MetaWu2077/Esp32_VoiceChat_LLMs/developboard/SmartAssistant-board/src/main/Audio1.cpp

#include "Audio1.h"

Audio1::Audio1()
{
  // 构造函数中仅做基本的初始化，不分配大块内存或其他可能引起问题的操作
  wavData = nullptr;
  i2s = nullptr;
  i2s = new I2S();

  // wavData = new char*[wavDataSize/dividedWavDataSize];
  // for (int i = 0; i < wavDataSize/dividedWavDataSize; ++i) wavData[i] = new char[dividedWavDataSize];
  // i2s = new I2S(micType);
}

Audio1::~Audio1()
{
  for (int i = 0; i < wavDataSize / dividedWavDataSize; ++i)
    delete[] wavData[i];
  delete[] wavData;
  delete i2s;
}

void Audio1::init()
{
  wavData = new char *[1];
  for (int i = 0; i < 1; ++i)
    wavData[i] = new char[1280];
}

void Audio1::clear()
{
  i2s->clear();
}

void Audio1::CreateWavHeader(byte *header, int waveDataSize)
{
  header[0] = 'R';
  header[1] = 'I';
  header[2] = 'F';
  header[3] = 'F';
  unsigned int fileSizeMinus8 = waveDataSize + 44 - 8;
  header[4] = (byte)(fileSizeMinus8 & 0xFF);
  header[5] = (byte)((fileSizeMinus8 >> 8) & 0xFF);
  header[6] = (byte)((fileSizeMinus8 >> 16) & 0xFF);
  header[7] = (byte)((fileSizeMinus8 >> 24) & 0xFF);
  header[8] = 'W';
  header[9] = 'A';
  header[10] = 'V';
  header[11] = 'E';
  header[12] = 'f';
  header[13] = 'm';
  header[14] = 't';
  header[15] = ' ';
  header[16] = 0x10; // linear PCM
  header[17] = 0x00;
  header[18] = 0x00;
  header[19] = 0x00;
  header[20] = 0x01; // linear PCM
  header[21] = 0x00;
  header[22] = 0x01; // monoral
  header[23] = 0x00;
  header[24] = 0x80; // sampling rate 16000
  header[25] = 0x3E;
  header[26] = 0x00;
  header[27] = 0x00;
  header[28] = 0x00; // Byte/sec = 16000x2x1 = 32000
  header[29] = 0x7D;
  header[30] = 0x00;
  header[31] = 0x00;
  header[32] = 0x02; // 16bit monoral
  header[33] = 0x00;
  header[34] = 0x10; // 16bit
  header[35] = 0x00;
  header[36] = 'd';
  header[37] = 'a';
  header[38] = 't';
  header[39] = 'a';
  header[40] = (byte)(waveDataSize & 0xFF);
  header[41] = (byte)((waveDataSize >> 8) & 0xFF);
  header[42] = (byte)((waveDataSize >> 16) & 0xFF);
  header[43] = (byte)((waveDataSize >> 24) & 0xFF);
}

void Audio1::Record()
{

  i2s->Read(i2sBuffer, i2sBufferSize);
  for (int i = 0; i < i2sBufferSize / 8; ++i)
  {
    wavData[0][2 * i] = i2sBuffer[8 * i + 2];
    wavData[0][2 * i + 1] = i2sBuffer[8 * i + 3];
  }

  // client.print("\r\n");

  // unsigned long startTime = millis();
  // while (_client->available() == 0)
  // {
  //   if (millis() - startTime > 5000)
  //   { // 5莽钮聣膰聨聲莽搂麓茅聫聝膹偶?
  //     Serial.println(">>> Client Timeout!");
  //     _client->stop();
  //     return "false";
  //   }
  // }
  // // Serial.println("123");
  // char c = 0;
  // int q = 0;

  // if (_client->available())
  // {
  //   String response = _client->readString();

  //   Serial.println(response);

  //   int jsonStartIndex = response.indexOf("\r\n\r\n") + 4;
  //   String jsonResponse = response.substring(jsonStartIndex);

  //   Question = parseJSON(jsonResponse.c_str());
  //   // int len = Question.length();
  //   // Question = Question.substring(0, (len - 1));
  //   // Question = "\"" + Question + "\"";
  //   Serial.println(Question);
  // }

  // Serial.println("456");

  // _client->stop();
  // return Question;
}

String Audio1::parseJSON(const char *jsonResponse)
{
  DynamicJsonDocument doc(1024);

  // 瑙ｆ瀽JSON鍝嶅簲
  DeserializationError error = deserializeJson(doc, jsonResponse);
  if (error)
  {
    Serial.print(F("deserializeJson() failed: "));
    Serial.println(error.f_str());
    return String("");
  }

  // 鎻愬彇骞惰繑鍥?"question"
  const char *question = doc["result"][0];
  return String(question);
}

float Audio1::calculateRMS(uint8_t *buffer, int bufferSize)
{
  float sum = 0;
  int16_t sample;

  // 每次迭代处理两个字节（16位）
  for (int i = 0; i < bufferSize; i += 2)
  {
    // 从缓冲区中获取16位样本，考虑到字节顺序
    sample = (buffer[i + 1] << 8) | buffer[i];

    // 计算样本的平方并累加
    sum += sample * sample;
  }

  // 计算平均值
  sum /= (bufferSize / 2);

  // 返回RMS值
  return sqrt(sum);
}
